ChefBenni/PTW-Electronics/ECU/V1.0 - Systema based/pictures/Altium ECAD V1.0.PNG

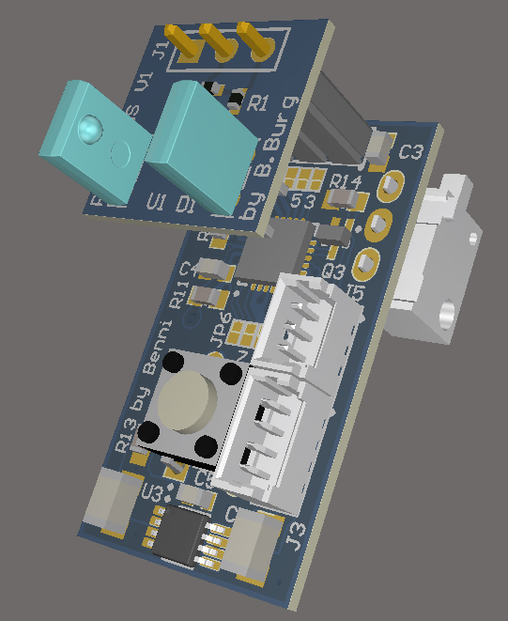
ECU/V1.0 - Systema based/pictures/Altium ECAD V1.0.PNG
