ChefBenni/PTW-Electronics/ECU/V1.0 - Systema based/pictures/Altium ECU ECAD V1.0_Top layer.PNG

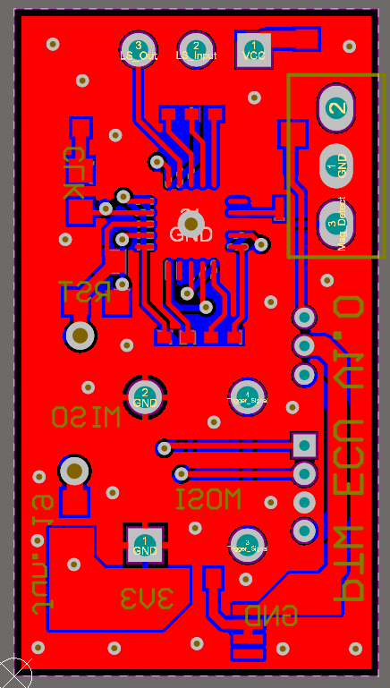
ECU/V1.0 - Systema based/pictures/Altium ECU ECAD V1.0_Top layer.PNG
