ChefBenni/PTW-Electronics/ECU/V1.0 - Systema based/pictures/Bed_of_needle.PNG

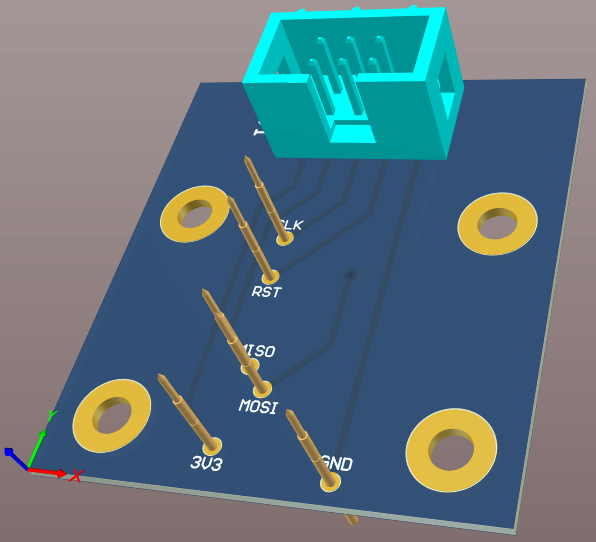
ECU/V1.0 - Systema based/pictures/Bed_of_needle.PNG
