ChefBenni/PTW-Electronics/ECU/V1.0 - Systema based/pictures/Bennis_ECU_V1_Period_Times.bmp

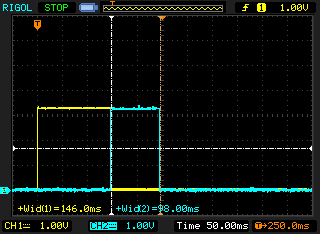
ECU/V1.0 - Systema based/pictures/Bennis_ECU_V1_Period_Times.bmp
