ChefBenni/PTW-Electronics/ECU/V1.0 - Systema based/pictures/Bennis_ECU_V1_Shot_through_voltages.bmp

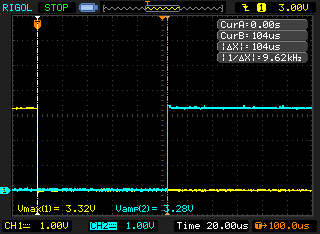
ECU/V1.0 - Systema based/pictures/Bennis_ECU_V1_Shot_through_voltages.bmp
