ChefBenni/PTW-Electronics/ECU/V1.0 - Systema based/pictures/IMG_3553.jpeg

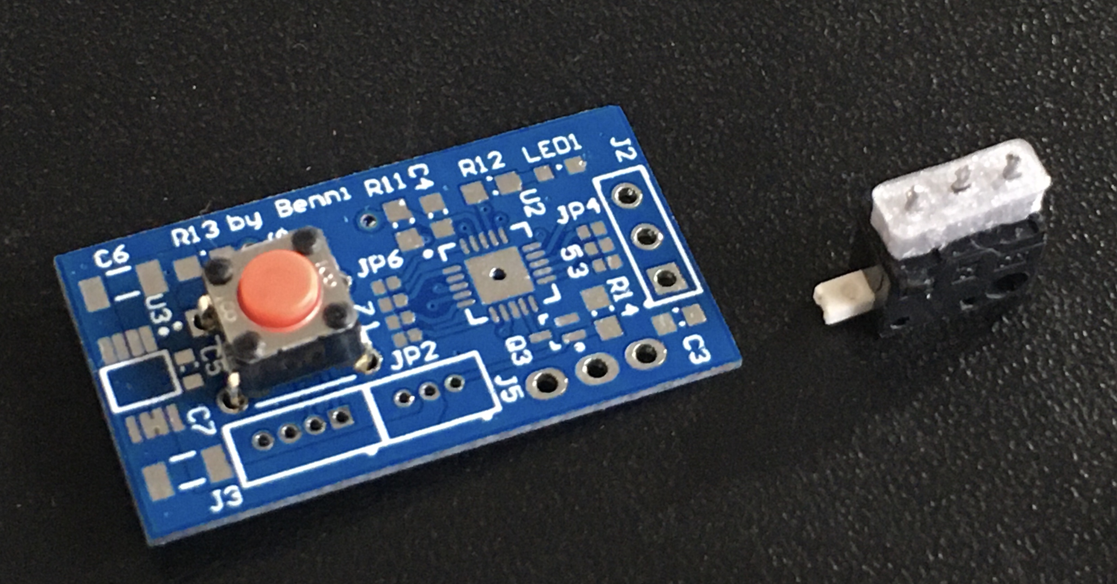
ECU/V1.0 - Systema based/pictures/IMG_3553.jpeg
