ChefBenni/PTW-Electronics/ECU/V1.0 - Systema based/pictures/USB-Connector.PNG

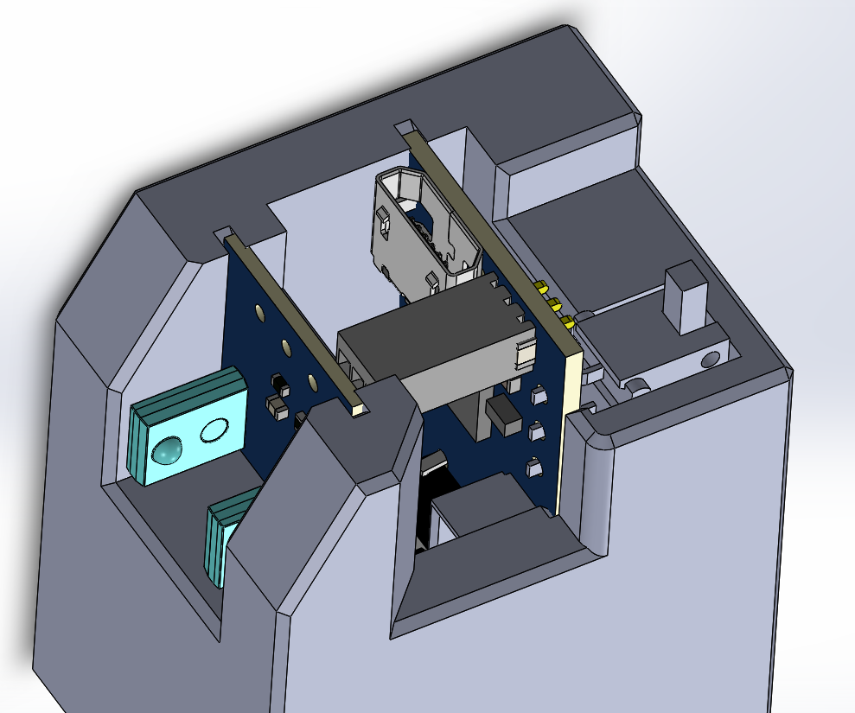
ECU/V1.0 - Systema based/pictures/USB-Connector.PNG
