ChefBenni/PTW-Electronics/Mosfet/Comparision mosfets.jpg

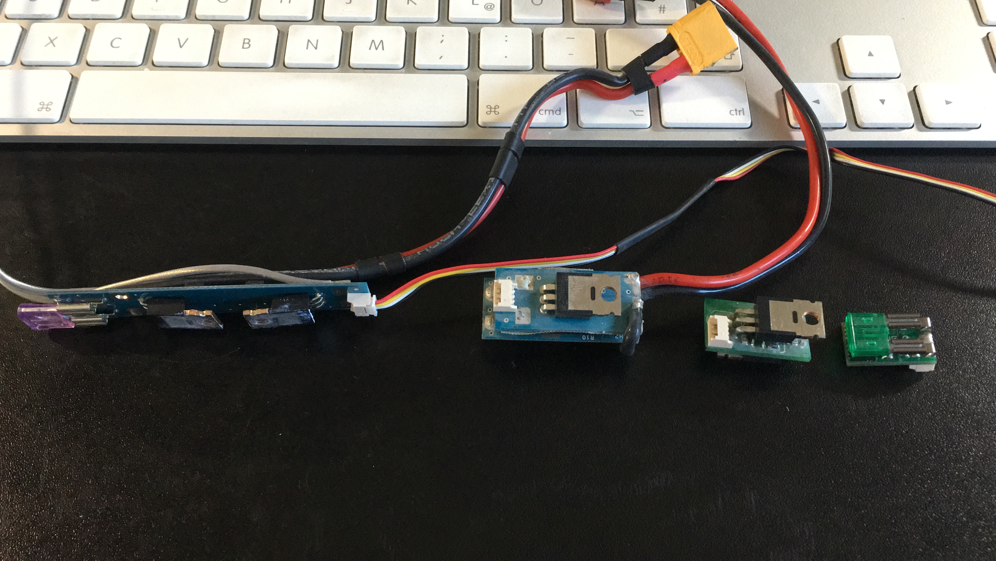
Mosfet/Comparision mosfets.jpg
