ChefBenni/PTW-Electronics/Mosfet/PTW_Idea_Elektronik_in_Stocktube.PNG

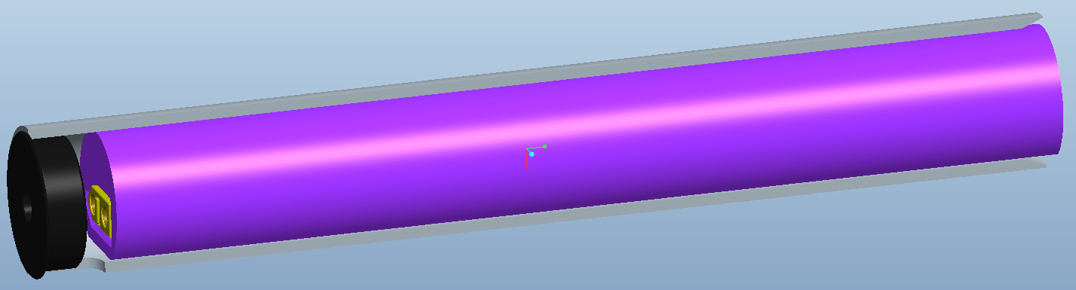
Mosfet/PTW_Idea_Elektronik_in_Stocktube.PNG
