ChefBenni/PTW-Electronics/Mosfet/V1.1 - basic design with fuse/pictures/Altium Mosfet ECAD V1.1_front.PNG

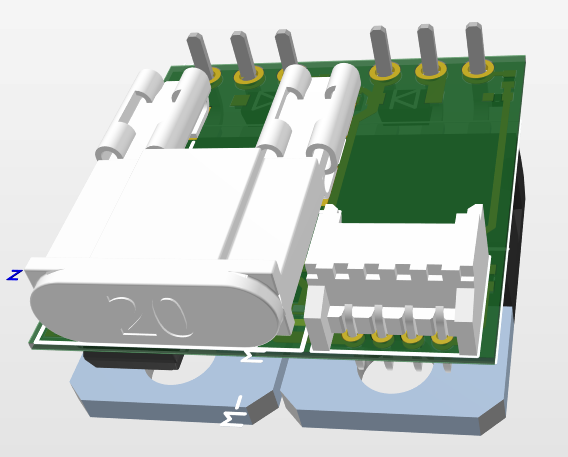
Mosfet/V1.1 - basic design with fuse/pictures/Altium Mosfet ECAD V1.1_front.PNG
