ChefBenni/PTW-Electronics/Mosfet/V2.1 - new mosfets with ESD/pictures/Altium Mosfet ECAD V2.1_back.PNG

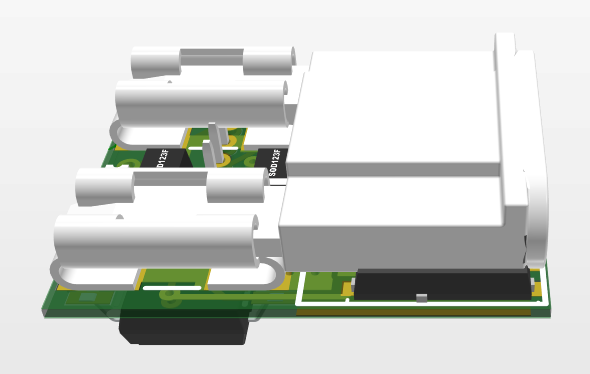
Mosfet/V2.1 - new mosfets with ESD/pictures/Altium Mosfet ECAD V2.1_back.PNG
