ChefBenni/PTW-Electronics/Mosfet/V2.1 - new mosfets with ESD/pictures/Altium Mosfet ECAD V2.1_front.PNG

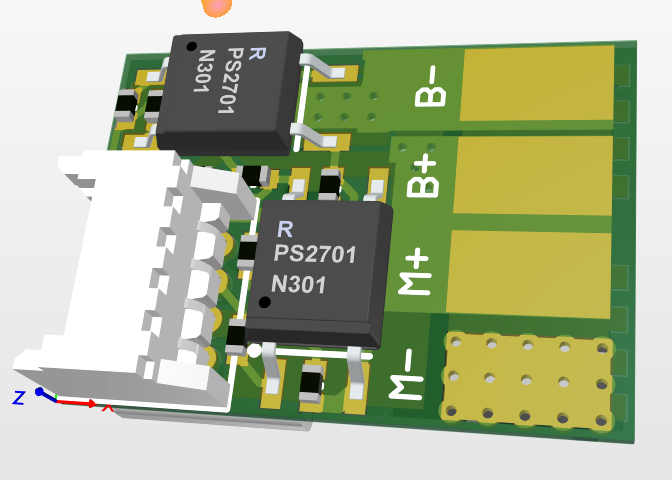
Mosfet/V2.1 - new mosfets with ESD/pictures/Altium Mosfet ECAD V2.1_front.PNG
