ChefBenni/PTW-Electronics/SENS/V1.0 - Initial version/pictures/Altium SENS ECAD V1.0_Top layer.PNG

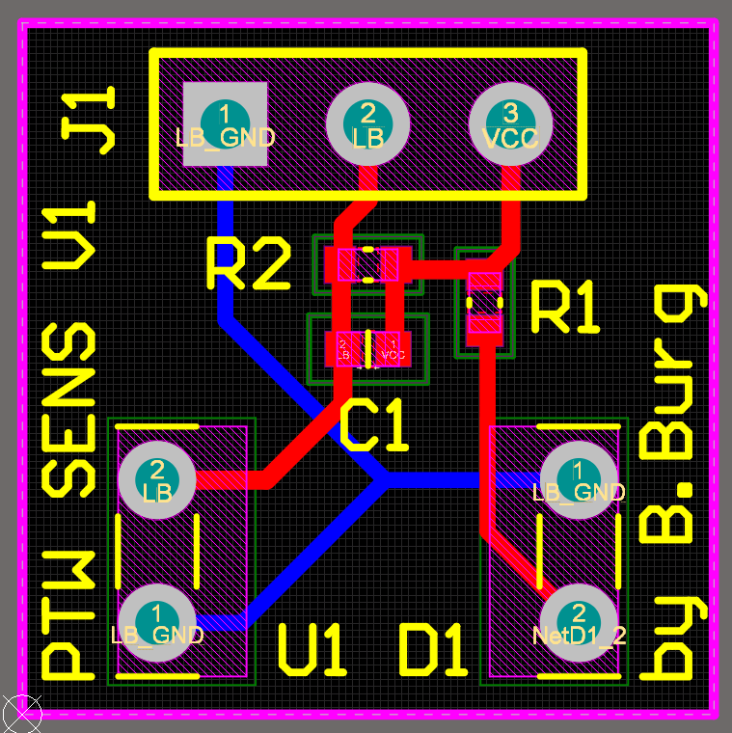
SENS/V1.0 - Initial version/pictures/Altium SENS ECAD V1.0_Top layer.PNG
