ChefBenni/PTW-Electronics/SENS/V1.0 - Initial version/pictures/SENS_Space_error.jpeg

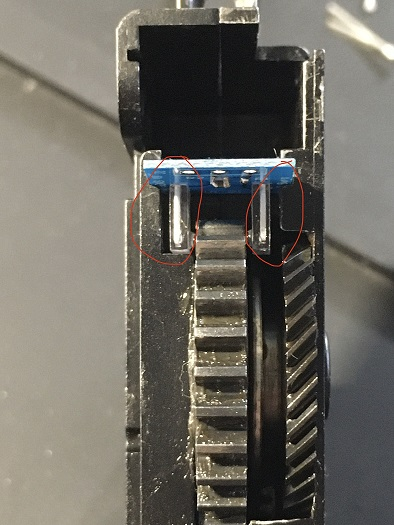
SENS/V1.0 - Initial version/pictures/SENS_Space_error.jpeg
