ChefBenni/PTW-Electronics/ECU/V1.0 - Systema based/pictures/Bench_setup_mess.JPG

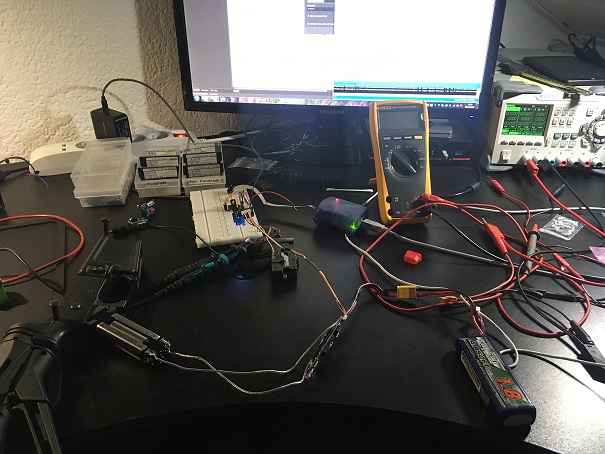
ECU/V1.0 - Systema based/pictures/Bench_setup_mess.JPG
