ChefBenni/PTW-Electronics/ECU/V1.0 - Systema based/pictures/ECU_assembled_front.JPEG

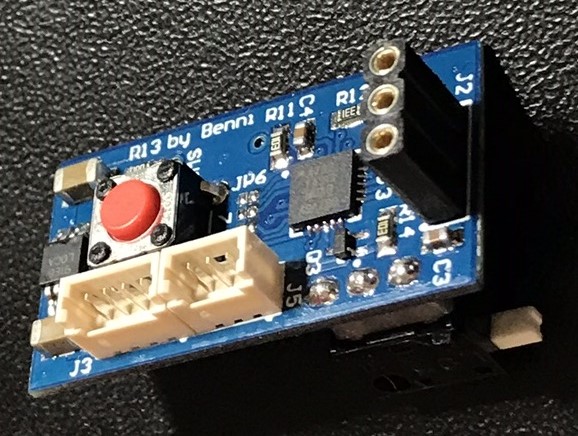
ECU/V1.0 - Systema based/pictures/ECU_assembled_front.JPEG
