ChefBenni/PTW-Electronics/ECU/V1.0 - Systema based/pictures/Soldering Fixture_Systema PCB.jpeg

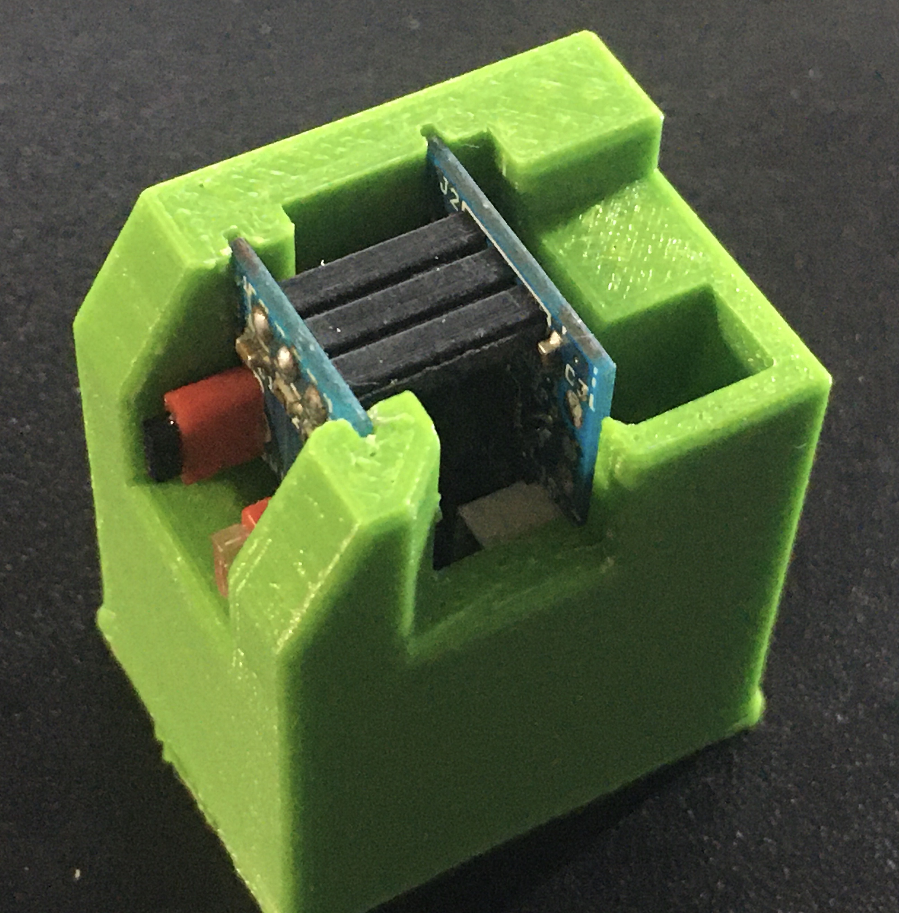
ECU/V1.0 - Systema based/pictures/Soldering Fixture_Systema PCB.jpeg
