ChefBenni/PTW-Electronics/Mosfet/V1.0 - basic design/pictures/Build Mosfet V1.0 front.JPG

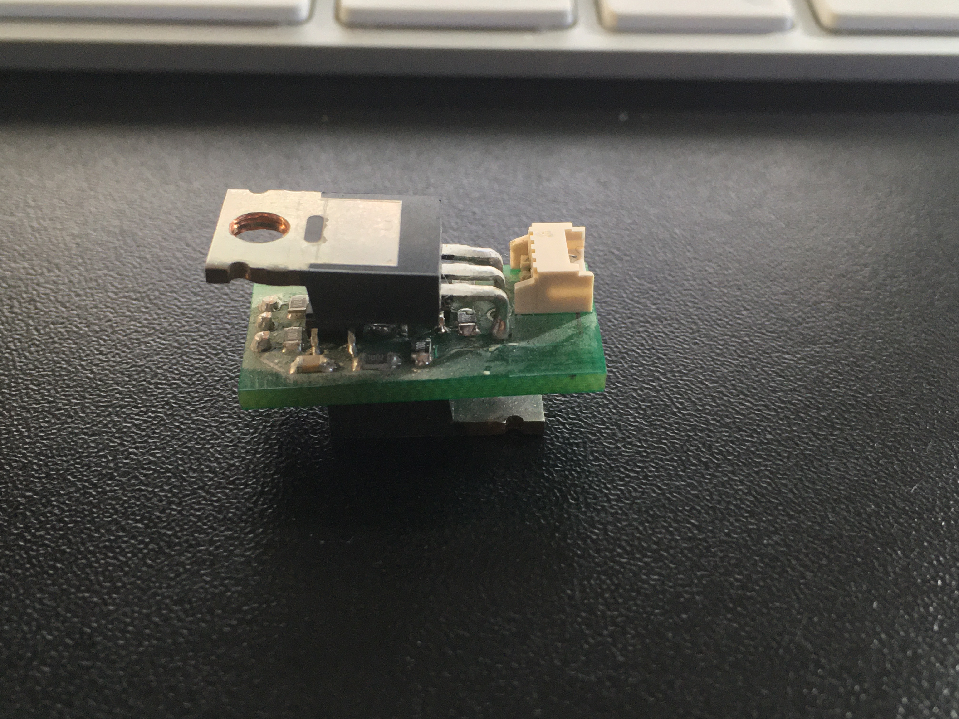
Mosfet/V1.0 - basic design/pictures/Build Mosfet V1.0 front.JPG
