ChefBenni/PTW-Electronics/Mosfet/V2.0 - new mosfets/pictures/Build Mosfet V2.0 front.JPG

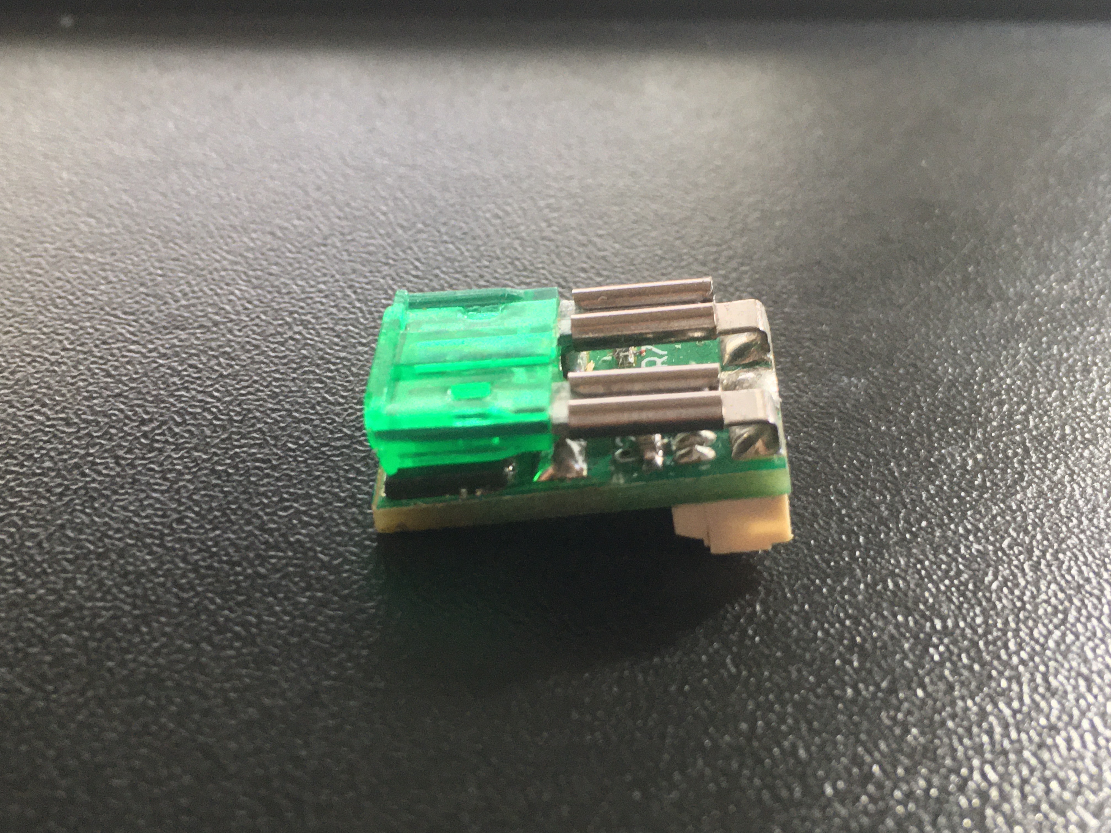
Mosfet/V2.0 - new mosfets/pictures/Build Mosfet V2.0 front.JPG
