ChefBenni/PTW-Electronics/ECU/V1.0 - Systema based/pictures/benchboard_test_succesful_IO.JPEG

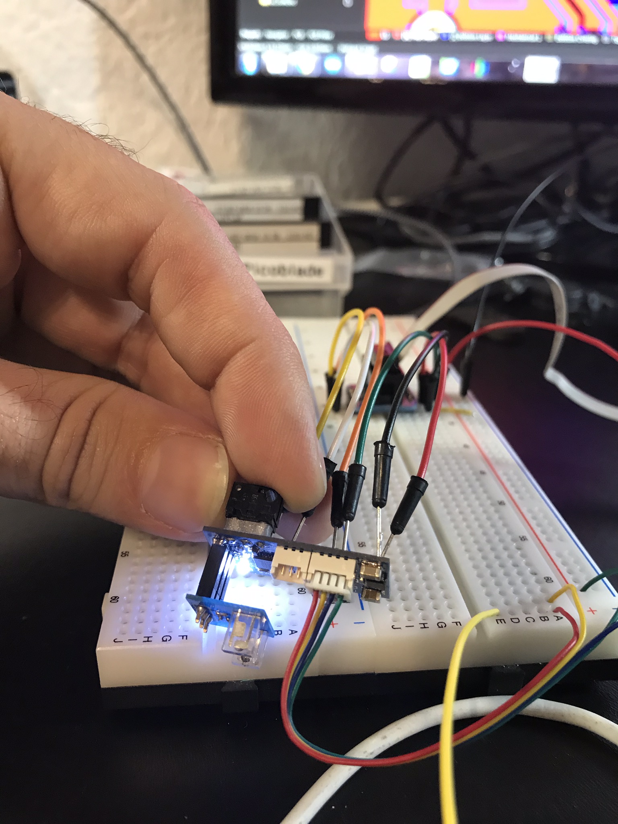
ECU/V1.0 - Systema based/pictures/benchboard_test_succesful_IO.JPEG
