ChefBenni/PTW-Electronics/ECU/V1.0 - Systema based/pictures/Fitting_and_function_test.jpeg

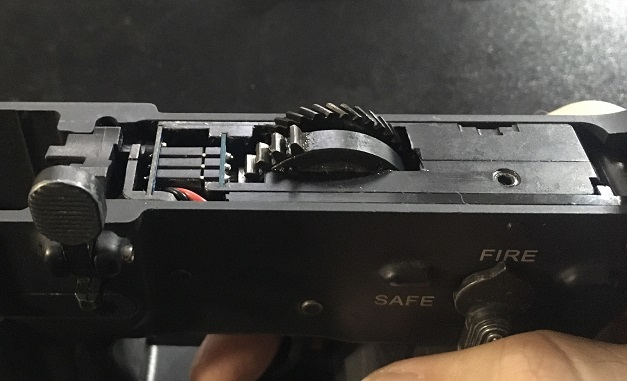
ECU/V1.0 - Systema based/pictures/Fitting_and_function_test.jpeg
