ChefBenni/PTW-Electronics/SENS/V1.0 - Initial version/pictures/SENS_Breadboard_test.JPG

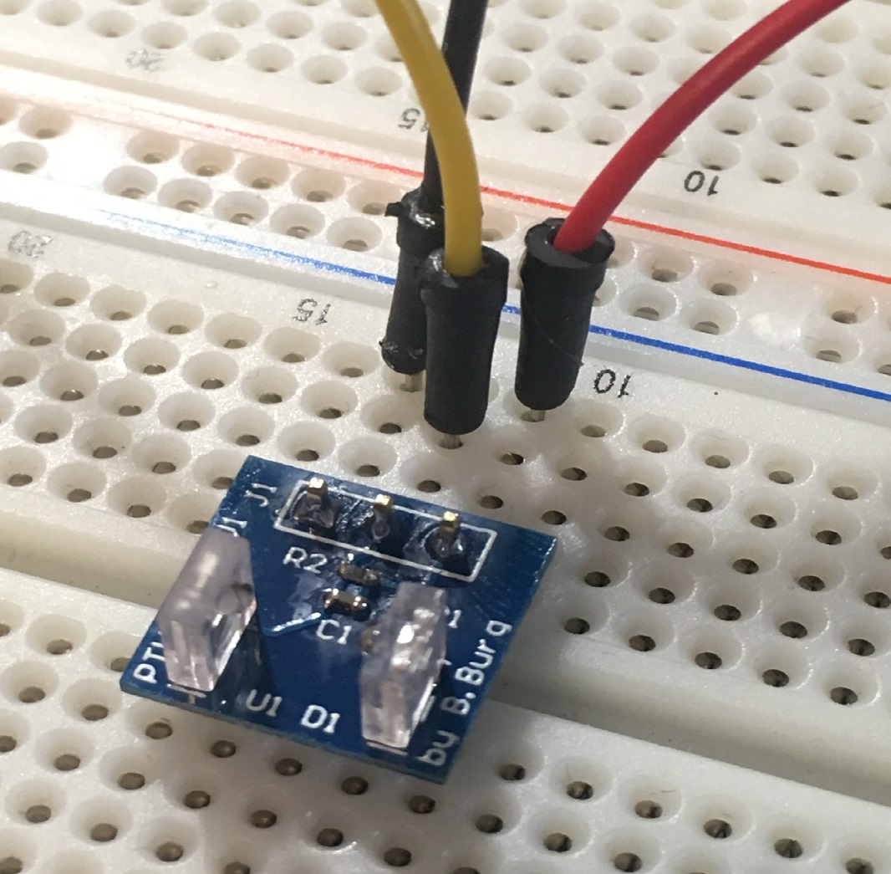
SENS/V1.0 - Initial version/pictures/SENS_Breadboard_test.JPG
