ChefBenni/PTW-Electronics/SENS/V1.0 - Initial version/pictures/SENS_Breadboard_test_Cycling.JPG

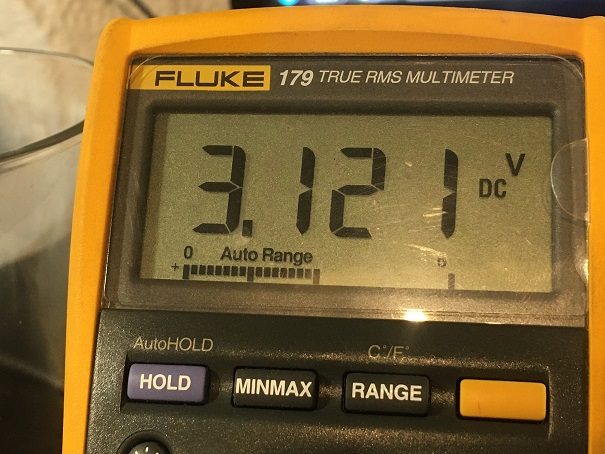
SENS/V1.0 - Initial version/pictures/SENS_Breadboard_test_Cycling.JPG
