ChefBenni/PTW-Electronics/SENS/V1.0 - Initial version/pictures/SENS_Breadboard_test_end_cycle.JPG

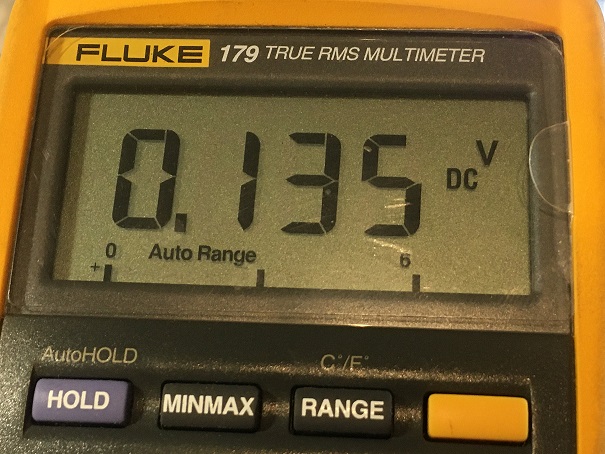
SENS/V1.0 - Initial version/pictures/SENS_Breadboard_test_end_cycle.JPG
